shadopawn/morse-code-watch/src/morse_code_watch/attiny_sleep.h

#include <Arduino.h>
#include <avr/sleep.h>

class ATtinySleep
{
    public:
        void sleep();

    private:
        void applySleepSettings();
        void disableAdc();
        void enterSleep();
    
};
