shadopawn/morse-code-watch/src/morse_code_watch/programmer_status.h

#include <Arduino.h>

class ProgrammerStatus
{
    public:
        ProgrammerStatus(int voltageThreshold = 4000);
        bool isProgrammerAttached();

    private:
        int voltageThreshold;
        int internalVoltage();
        unsigned int unscaledVoltageReading();
};
