shadopawn/morse-code-watch/src/morse_code_watch/low_power_rtc.h

#pragma once

#include <DS3232RTC.h>

class LowPowerRtc
{
    public:
        LowPowerRtc(byte rtcPowerPin);
        void syncWithRtc();
        void setTime(time_t time);

    private:
        byte rtcPowerPin;
};
