shadopawn/morse-code-watch/examples/software_serial/software_serial.ino

#include <SoftwareSerial.h>
// ***
// *** Define the RX and TX pins. Choose any two
// *** pins that are unused. Try to avoid D0 (pin 5)
// *** and D2 (pin 7) if you plan to use I2C.
// ***
#define RX    3   // *** D3, Pin 2
#define TX    4   // *** D4, Pin 3

// ***
// *** Define the software based serial port. Using the
// *** name Serial so that code can be used on other
// *** platforms that support hardware based serial. On
// *** chips that support the hardware serial, just
// *** comment this line.
// ***
SoftwareSerial Serial(RX, TX);

void setup() {
  // put your setup code here, to run once:
  Serial.begin(9600);
  Serial.println("Initializing...");
}

void loop() {
  // put your main code here, to run repeatedly:
  Serial.println("Testing 1 2 3");
  delay(500);
}
